ElyOshri/DIY-Simulator-Stick-Shift/Hardware/Base Left.stl

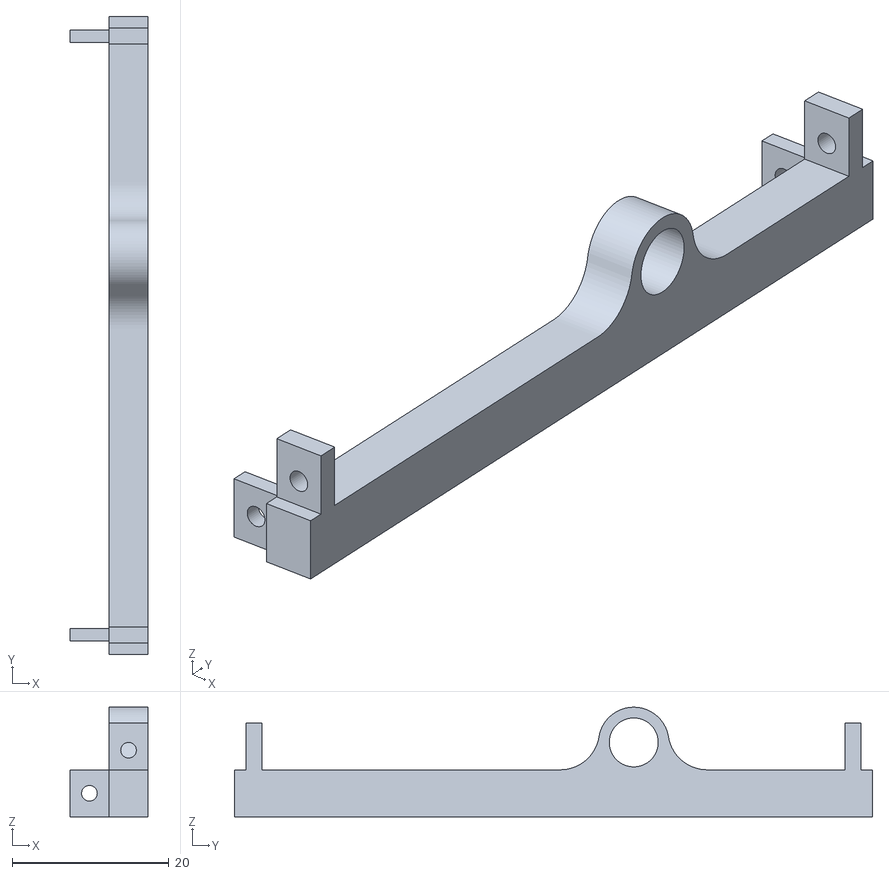
[picture p16: CAD file, 2021-09-07]
Hardware/Base Left.stl
10.0 x 81.5 x 14.0
